jac-oblong/JML/peripherals/jml-8-mini-vga/src/videoram.v

/*
 * At the beginning of the current line, prepares all pixels for the next line
 */

module videoram (
    input                    visible,
    input [HCOUNT_BITSREQ:0] horicount,
    input [VCOUNT_BITSREQ:0] vertcount,

    output [7:0] character
);

   `include "vgaspecs.vh"

   // videoram holds all which character to be displayed
   reg [7:0] ram[0:VTILES-1][0:HTILES-1];
   initial $readmemh("videoram.txt", ram, 0);

   wire [HTILES_BITSREQ:0] horioffset;
   wire [VTILES_BITSREQ:0] vertoffset;

   assign horioffset = horicount[HCOUNT_BITSREQ:3];
   assign vertoffset = vertcount[VCOUNT_BITSREQ-1:3];

   assign character  = visible ? ram[vertoffset][horioffset] : 0;

endmodule
